pablorj10/ProyectoTFG/Altium/TFG_Dispositivo/PCB_Dispositivo1.jpg

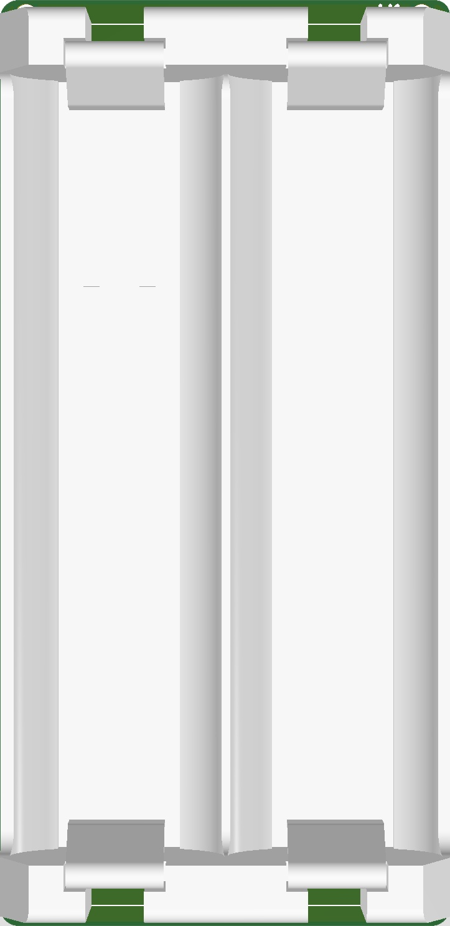
Altium/TFG_Dispositivo/PCB_Dispositivo1.jpg
