pablorj10/ProyectoTFG/Altium/TFG_Dispositivo/PCB_Dispositivo.jpg

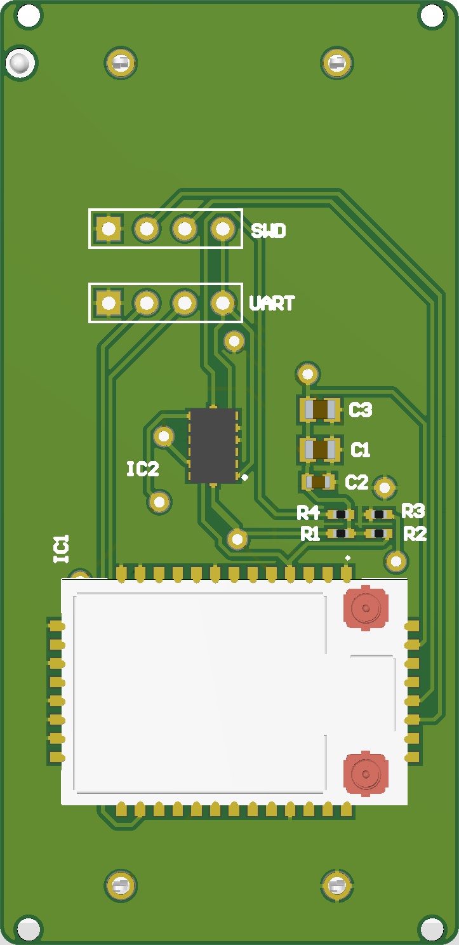
Altium/TFG_Dispositivo/PCB_Dispositivo.jpg
