pablorj10/ProyectoTFG/SolidWork/Fotos/Captura4.JPG

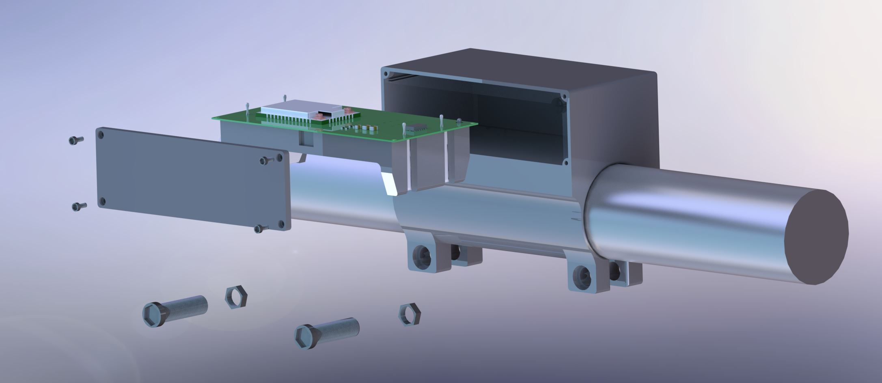
SolidWork/Fotos/Captura4.JPG
