pablorj10/ProyectoTFG/SolidWork/Fotos/Captura.JPG

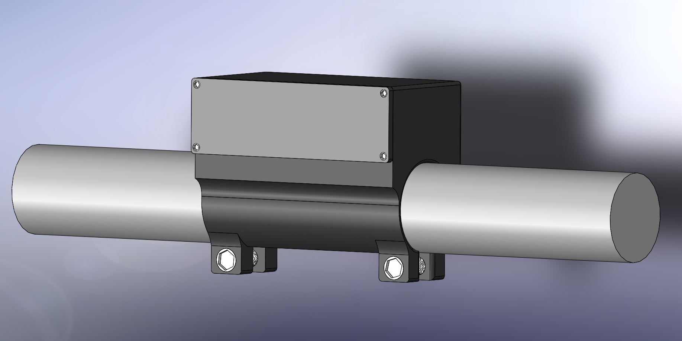
SolidWork/Fotos/Captura.JPG
