pablorj10/ProyectoTFG/SolidWork/Fotos/REnder1.JPG

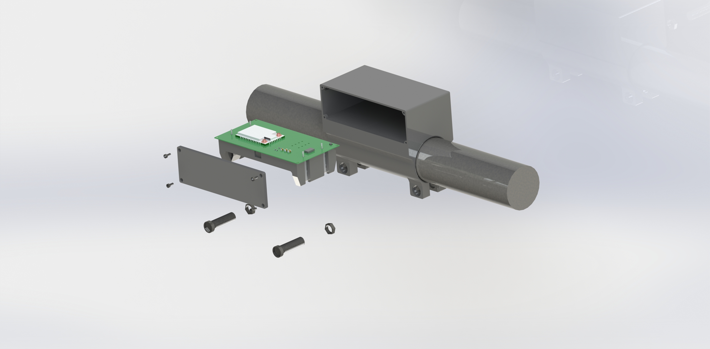
SolidWork/Fotos/REnder1.JPG
